speedbird620/Yet-another-simulator-chair/dxf/D1a.dxf

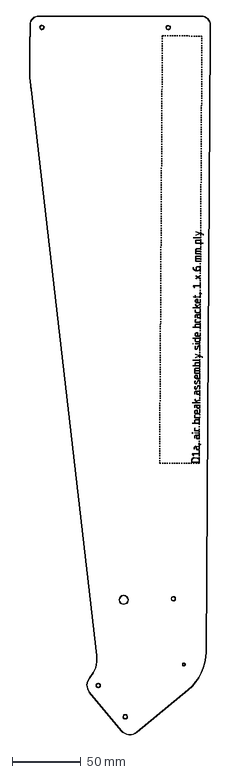
[picture p16: CAD file, 2024-12-31]
dxf/D1a.dxf
130.9 x 521.2 mm
