speedbird620/Yet-another-simulator-chair/stl/F12.stl

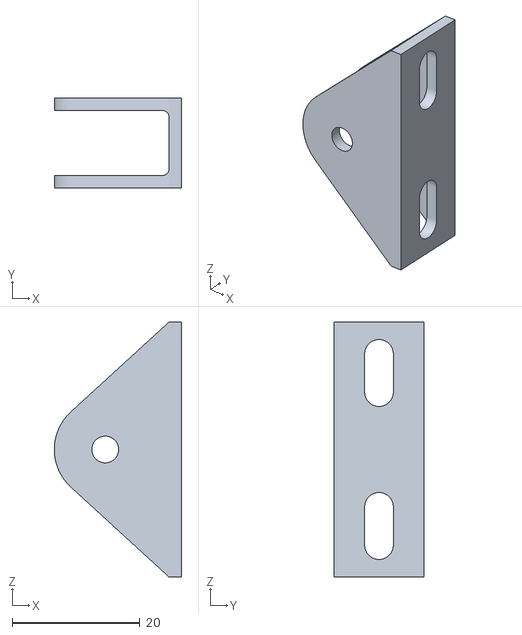
[picture p17: CAD file, 2025-11-08]
stl/F12.stl
20.0 x 14.2 x 40.0
