speedbird620/Yet-another-simulator-chair/dxf/A5.dxf

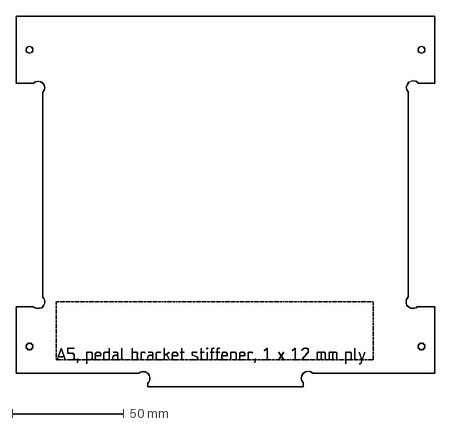
[picture p18: CAD file, 2024-12-29]
dxf/A5.dxf
187.7 x 166.0 mm
