speedbird620/Yet-another-simulator-chair/stl/F3.stl

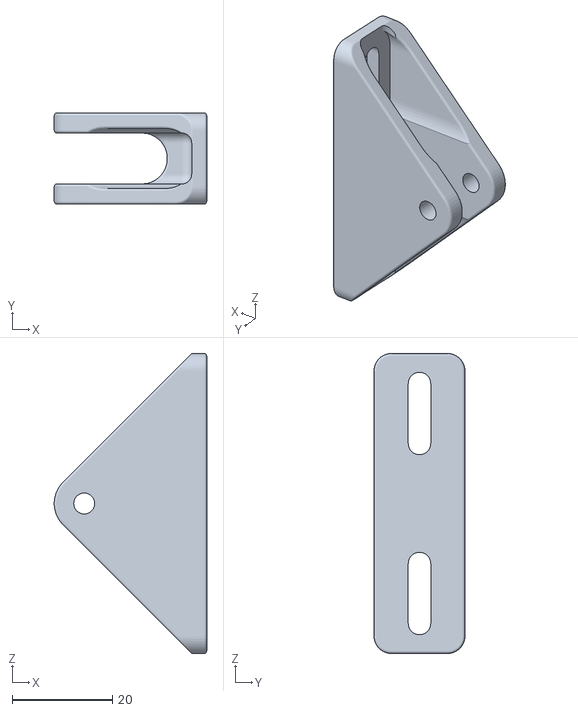
[picture p19: CAD file, 2025-11-08]
stl/F3.stl
30.5 x 18.2 x 60.0
