speedbird620/Yet-another-simulator-chair/dxf/B10.dxf

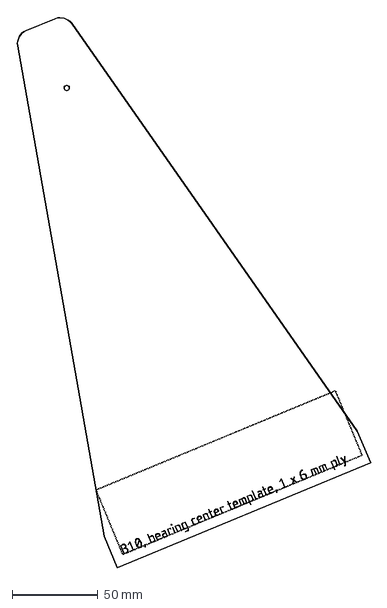
[picture p20: CAD file, 2024-12-22]
dxf/B10.dxf
206.6 x 321.9 mm
