speedbird620/Yet-another-simulator-chair/stl/H1.stl

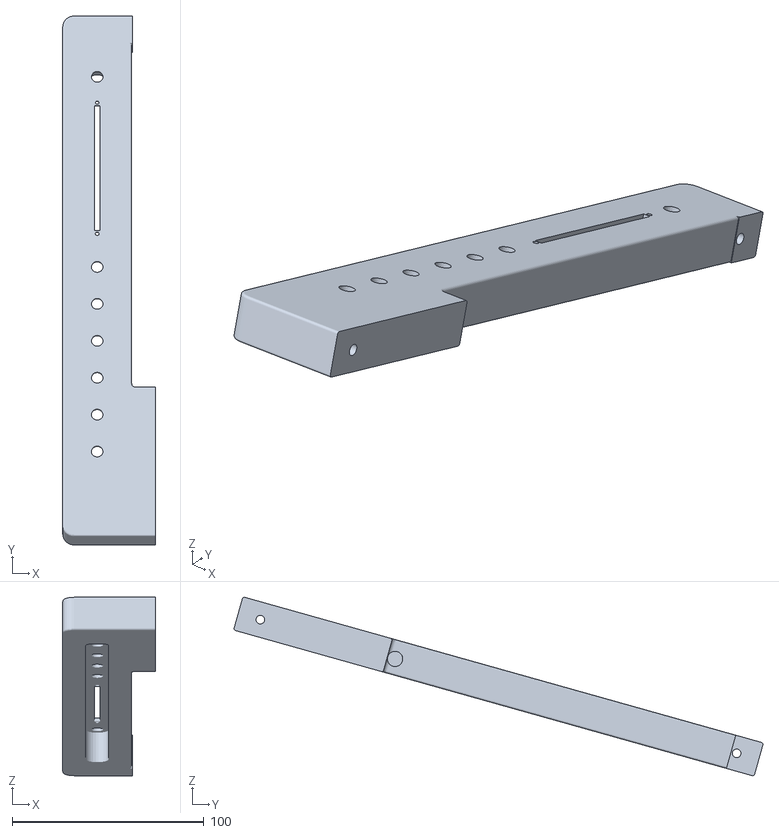
[picture p21: CAD file, 2025-10-26]
stl/H1.stl
48.3 x 275.9 x 93.1
