speedbird620/Yet-another-simulator-chair/dxf/C2.dxf

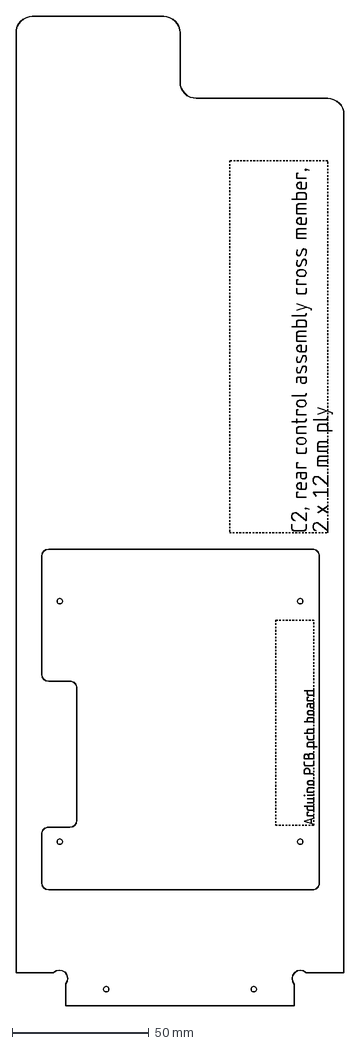
[picture p22: CAD file, 2024-12-13]
dxf/C2.dxf
120.0 x 362.0 mm
