speedbird620/Yet-another-simulator-chair/stl/H5.stl

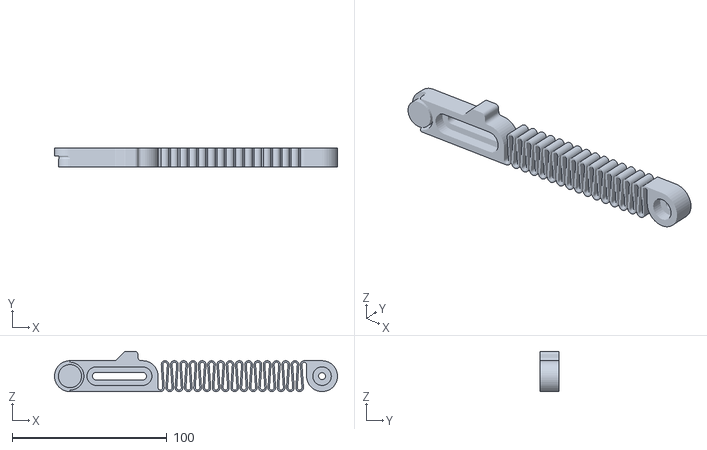
[picture p23: CAD file, 2024-12-18]
stl/H5.stl
183.0 x 12.0 x 26.0
