speedbird620/Yet-another-simulator-chair/dxf/B3.dxf

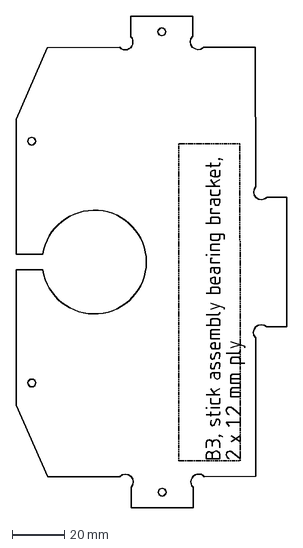
[picture p24: CAD file, 2024-12-13]
dxf/B3.dxf
104.1 x 188.9 mm
