speedbird620/Yet-another-simulator-chair/stl/H7.stl

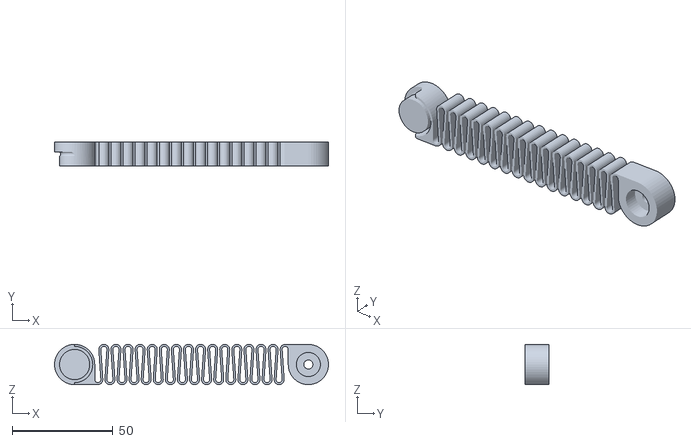
[picture p25: CAD file, 2024-12-18]
stl/H7.stl
136.0 x 12.0 x 20.0
