speedbird620/Yet-another-simulator-chair/dxf/A2.dxf

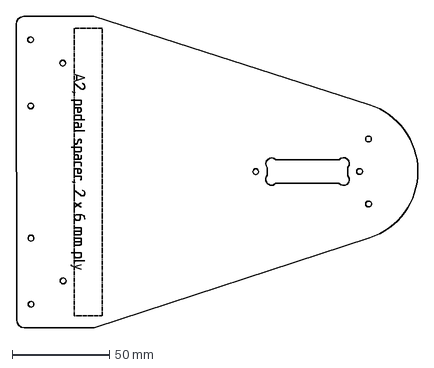
[picture p26: CAD file, 2024-12-13]
dxf/A2.dxf
206.7 x 160.1 mm
