speedbird620/Yet-another-simulator-chair/stl/F8.stl

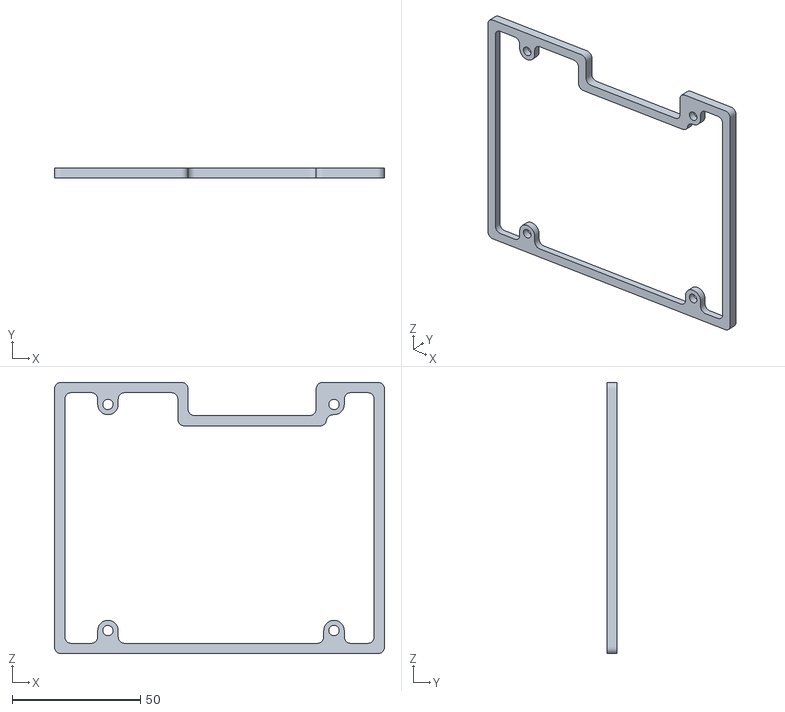
[picture p27: CAD file, 2024-12-17]
stl/F8.stl
128.5 x 4.00 x 105.6
