speedbird620/Yet-another-simulator-chair/dxf/B1.dxf

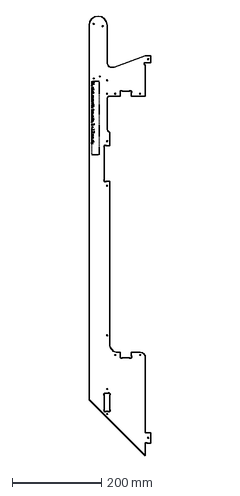
[picture p28: CAD file, 2024-12-13]
dxf/B1.dxf
138.0 x 985.4 mm
