speedbird620/Yet-another-simulator-chair/stl/H4.stl

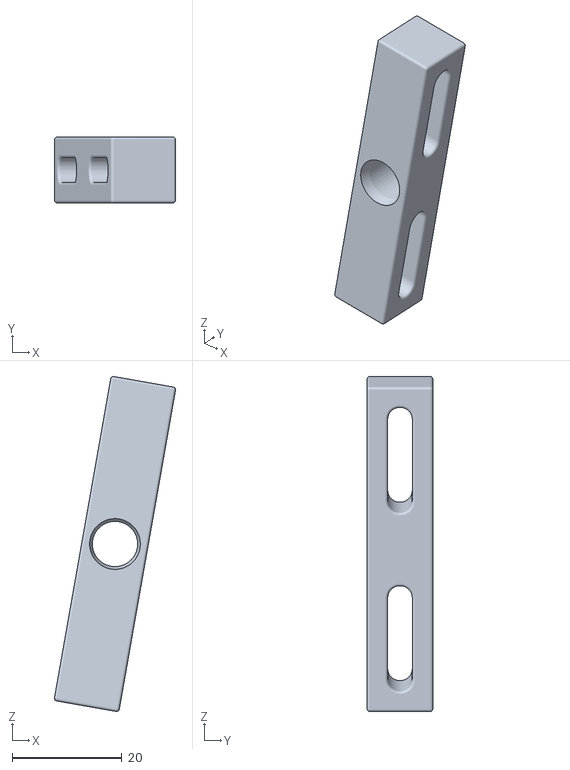
[picture p29: CAD file, 2024-12-15]
stl/H4.stl
22.1 x 12.0 x 61.0
