speedbird620/Yet-another-simulator-chair/dxf/A4.dxf

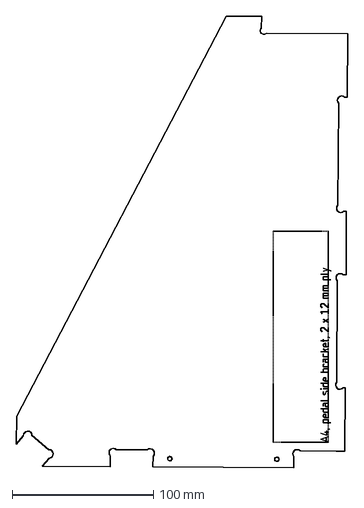
[picture p30: CAD file, 2024-12-13]
dxf/A4.dxf
234.7 x 320.0 mm
