speedbird620/Yet-another-simulator-chair/stl/H3.stl

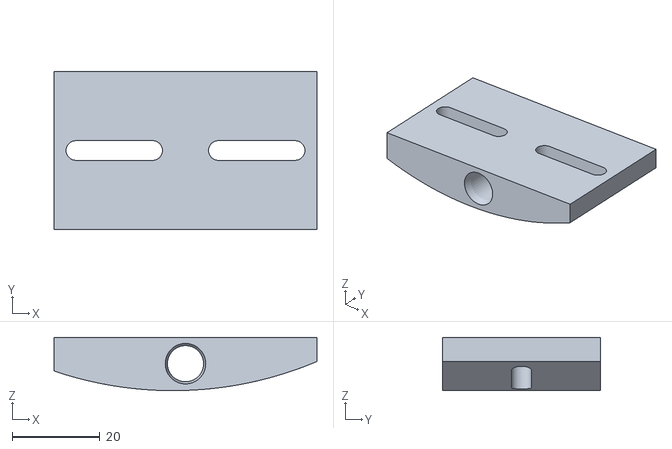
[picture p31: CAD file, 2024-12-15]
stl/H3.stl
60.0 x 36.0 x 12.1
