speedbird620/Yet-another-simulator-chair/dxf/B7.dxf

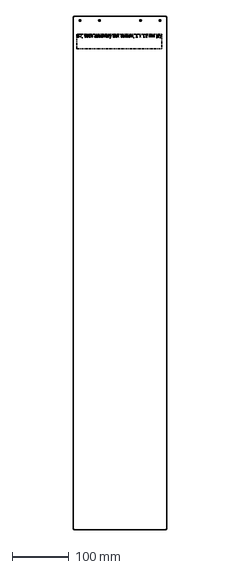
[picture p32: CAD file, 2024-12-13]
dxf/B7.dxf
165.0 x 906.5 mm
