speedbird620/Yet-another-simulator-chair/stl/G1.stl

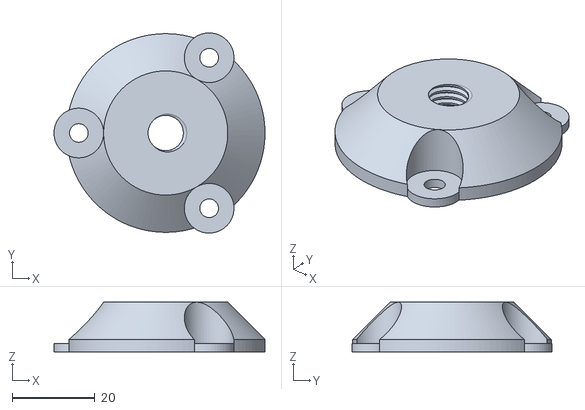
[picture p33: CAD file, 2024-12-07]
stl/G1.stl
51.0 x 48.4 x 12.0
