speedbird620/Yet-another-simulator-chair/dxf/C3.dxf

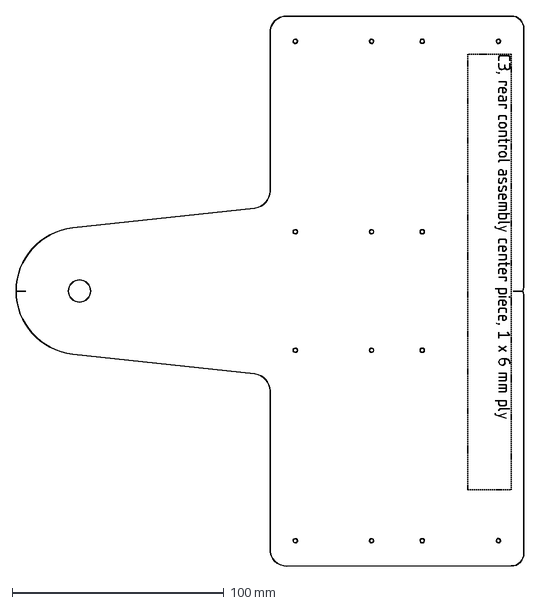
[picture p34: CAD file, 2024-12-13]
dxf/C3.dxf
240.0 x 260.0 mm
