speedbird620/Yet-another-simulator-chair/stl/F5.stl

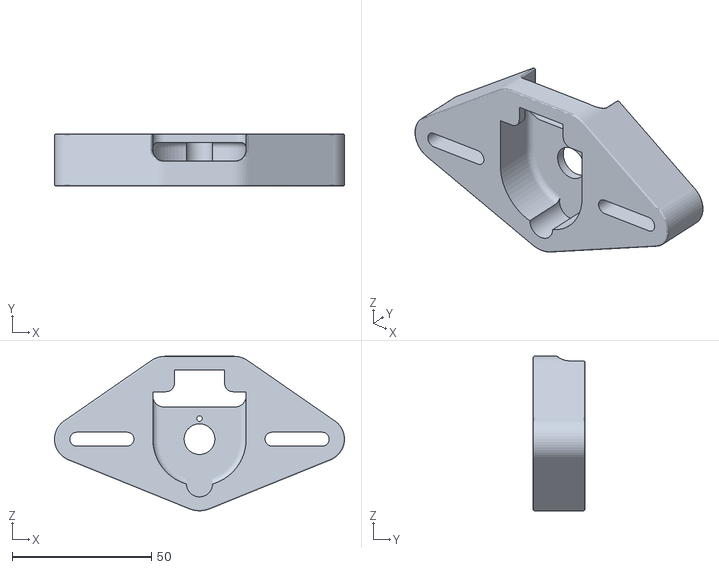
[picture p35: CAD file, 2024-12-04]
stl/F5.stl
104.0 x 18.6 x 55.4
