speedbird620/Yet-another-simulator-chair/dxf/E9.dxf

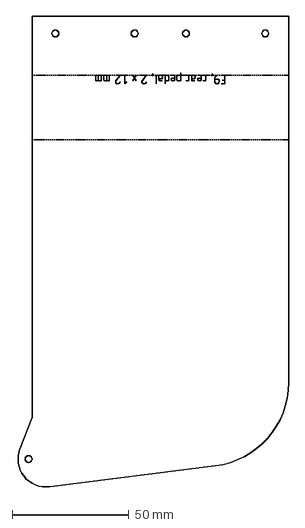
[picture p36: CAD file, 2024-12-13]
dxf/E9.dxf
116.7 x 202.4 mm
