speedbird620/Yet-another-simulator-chair/stl/G3.stl

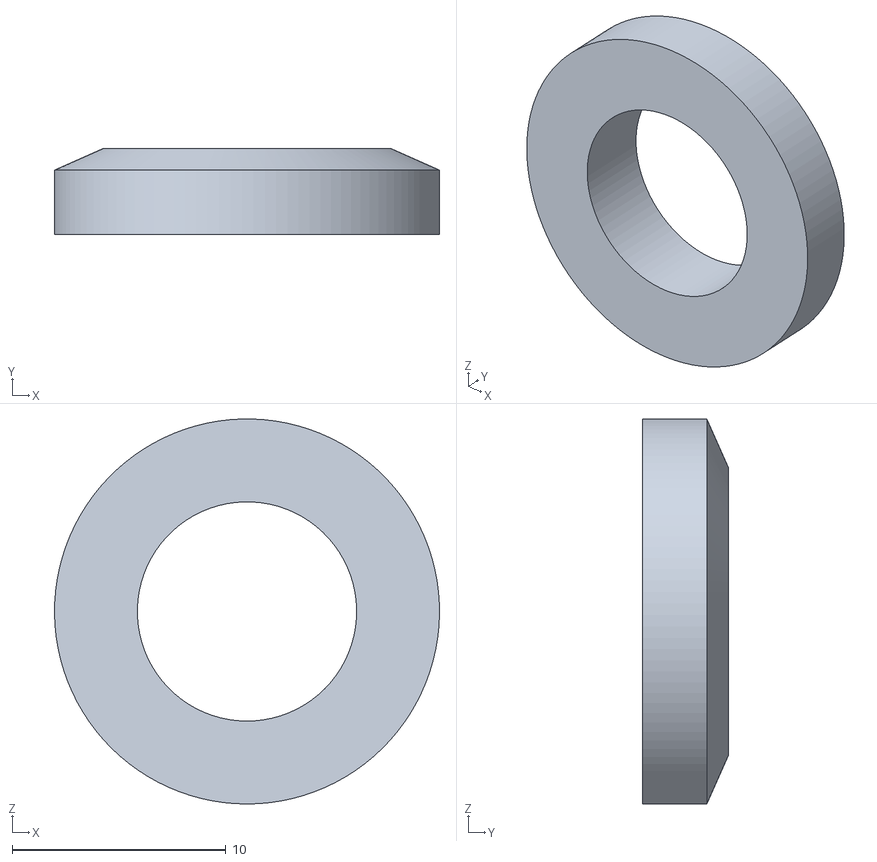
[picture p37: CAD file, 2024-12-03]
stl/G3.stl
18.0 x 4.00 x 18.0
