speedbird620/Yet-another-simulator-chair/dxf/B5.dxf

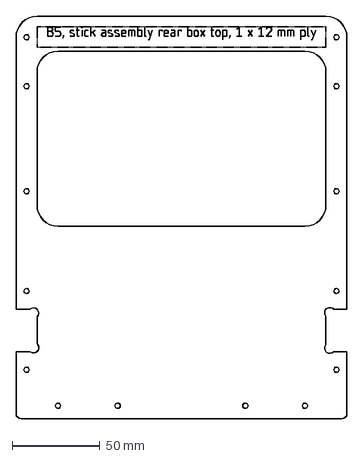
[picture p38: CAD file, 2024-12-13]
dxf/B5.dxf
189.0 x 230.0 mm
