speedbird620/Yet-another-simulator-chair/stl/G2.stl

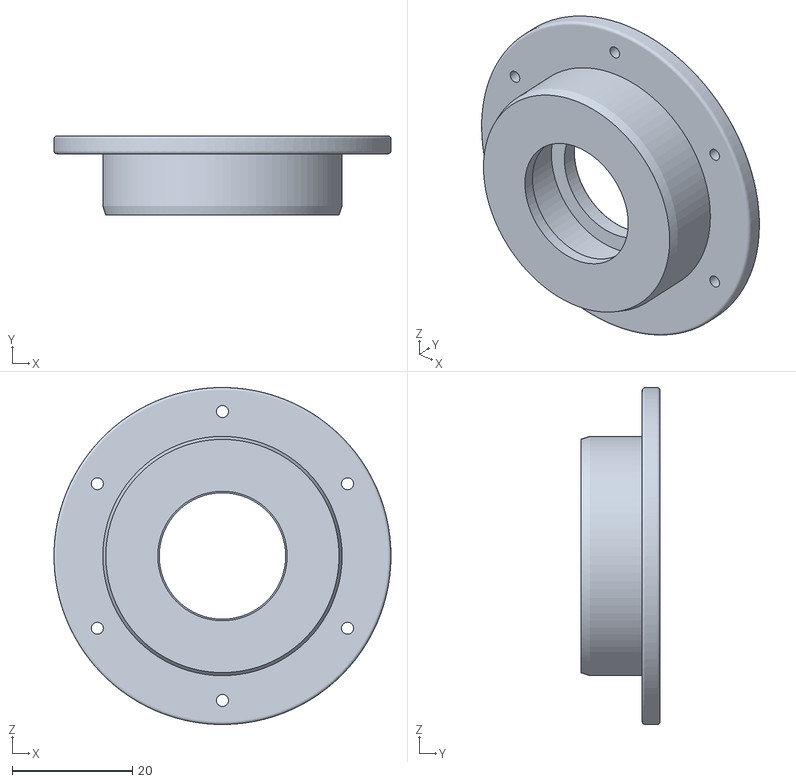
[picture p39: CAD file, 2024-12-03]
stl/G2.stl
56.0 x 13.2 x 56.0
