speedbird620/Yet-another-simulator-chair/dxf/E1.dxf

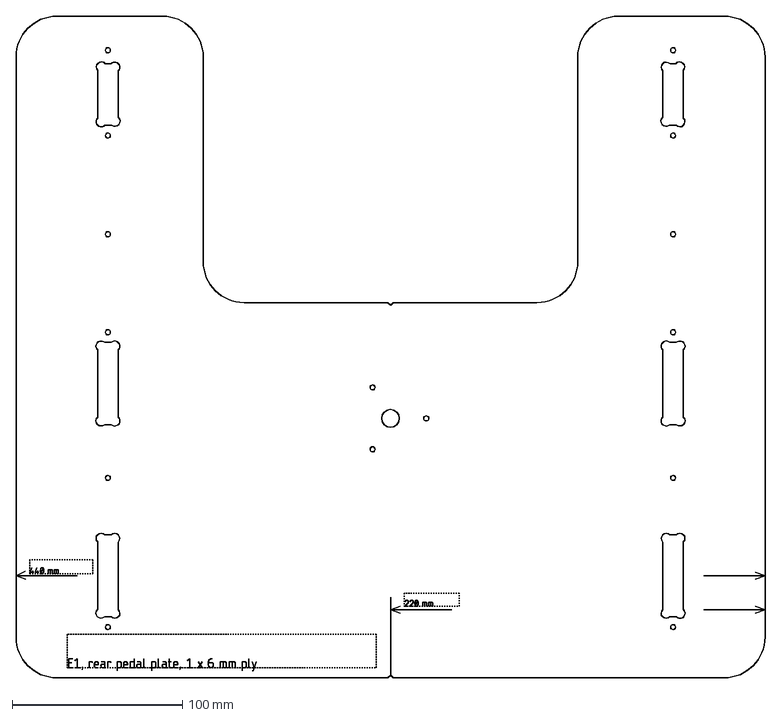
[picture p40: CAD file, 2024-12-13]
dxf/E1.dxf
440.0 x 388.7 mm
