speedbird620/Yet-another-simulator-chair/stl/F4.stl

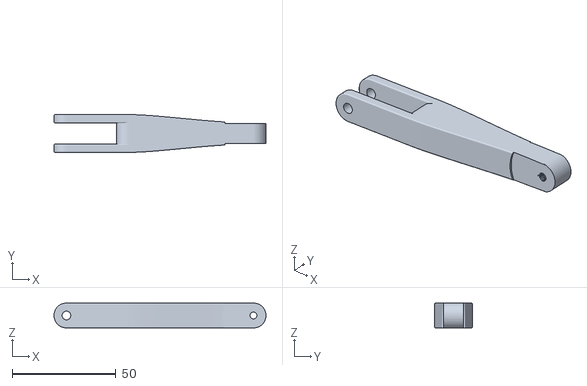
[picture p41: CAD file, 2024-12-03]
stl/F4.stl
102.0 x 18.2 x 12.0
