speedbird620/Yet-another-simulator-chair/dxf/E7.dxf

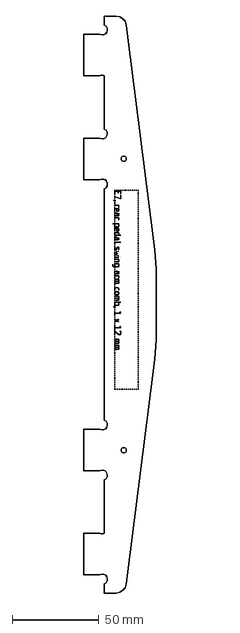
[picture p42: CAD file, 2024-12-13]
dxf/E7.dxf
42.0 x 333.1 mm
