speedbird620/Yet-another-simulator-chair/stl/F2.stl

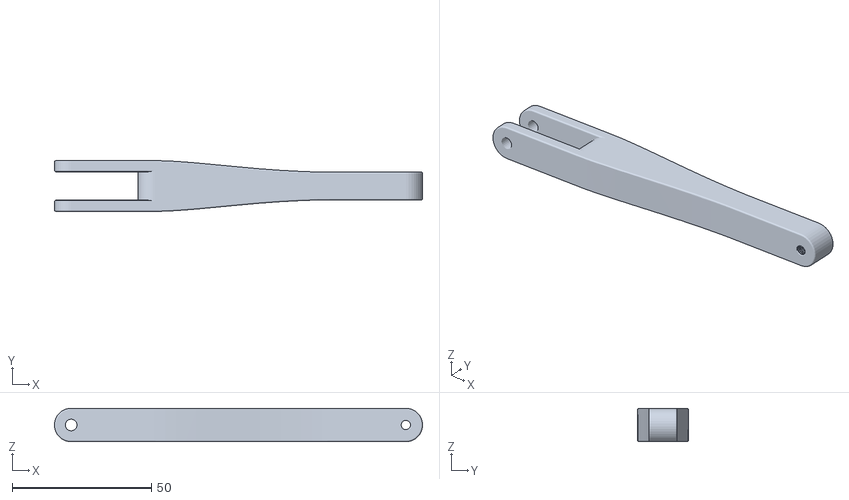
[picture p43: CAD file, 2024-08-14]
stl/F2.stl
132.0 x 18.2 x 12.0
