speedbird620/Yet-another-simulator-chair/dxf/E6.dxf

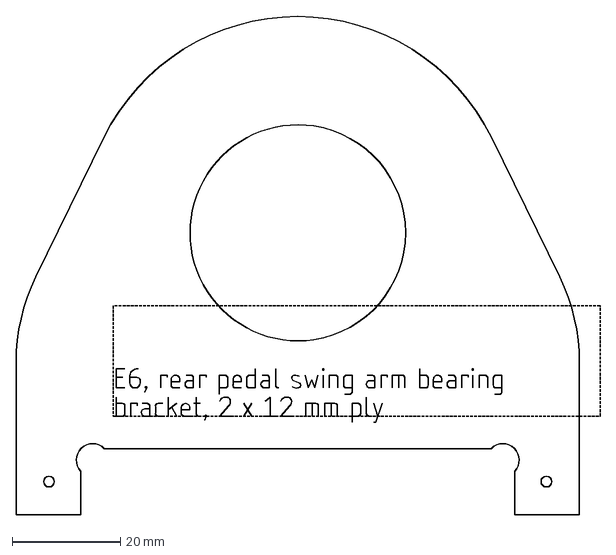
[picture p44: CAD file, 2024-12-13]
dxf/E6.dxf
108.0 x 92.1 mm
