speedbird620/Yet-another-simulator-chair/dxf/A6.dxf

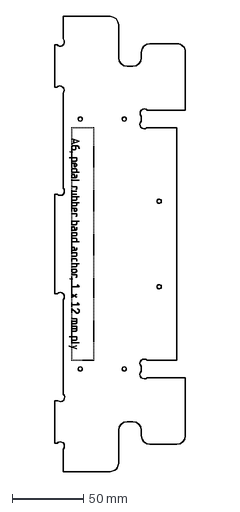
[picture p45: CAD file, 2024-12-13]
dxf/A6.dxf
92.0 x 320.0 mm
