speedbird620/Yet-another-simulator-chair/dxf/A8.dxf

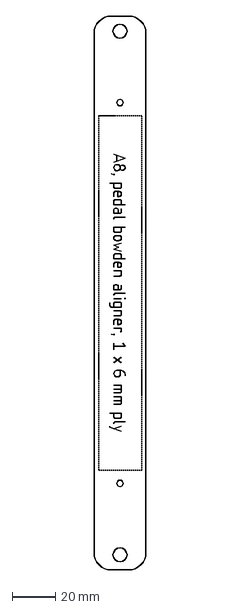
[picture p46: CAD file, 2024-12-13]
dxf/A8.dxf
24.0 x 255.7 mm
