speedbird620/Yet-another-simulator-chair/dxf/D5.dxf

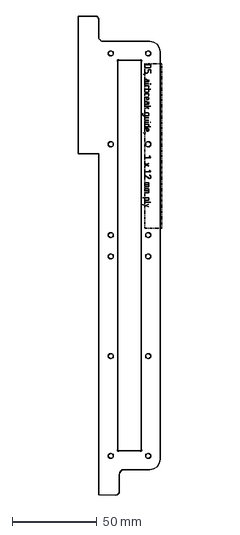
[picture p47: CAD file, 2024-12-13]
dxf/D5.dxf
49.2 x 282.0 mm
