speedbird620/Yet-another-simulator-chair/dxf/A7.dxf

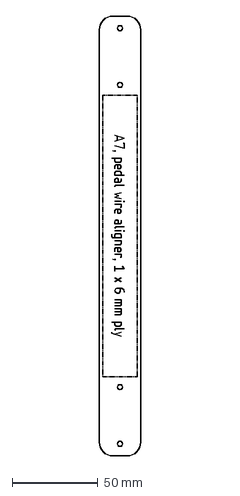
[picture p48: CAD file, 2024-12-13]
dxf/A7.dxf
24.0 x 255.7 mm
