speedbird620/Yet-another-simulator-chair/dxf/A1.dxf

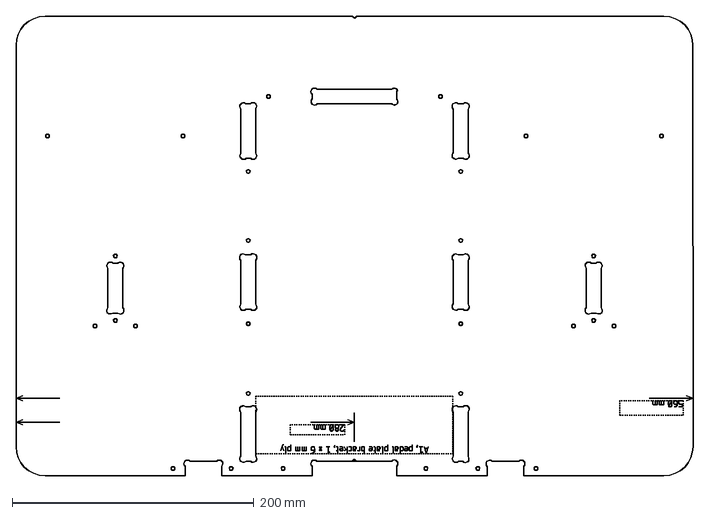
[picture p49: CAD file, 2024-12-13]
dxf/A1.dxf
560.0 x 380.0 mm
