speedbird620/Yet-another-simulator-chair/dxf/C1.dxf

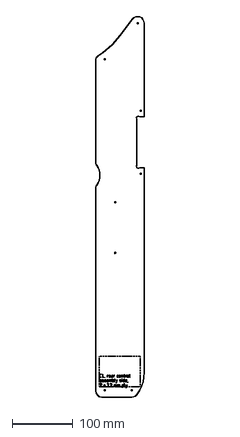
[picture p50: CAD file, 2024-12-13]
dxf/C1.dxf
80.0 x 628.1 mm
