speedbird620/Yet-another-simulator-chair/dxf/D1.dxf

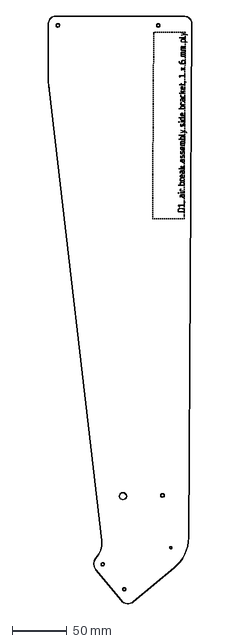
[picture p51: CAD file, 2024-12-13]
dxf/D1.dxf
130.9 x 535.2 mm
