speedbird620/Yet-another-simulator-chair/dxf/D6.dxf

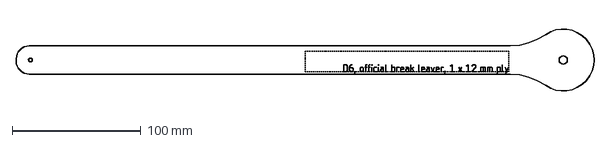
[picture p52: CAD file, 2024-12-13]
dxf/D6.dxf
451.0 x 53.3 mm
