speedbird620/Yet-another-simulator-chair/dxf/E3.dxf

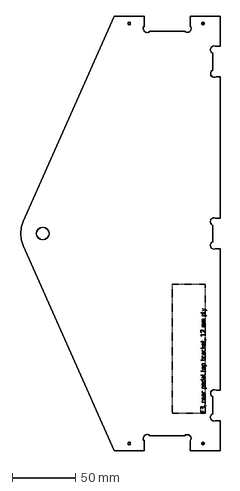
[picture p53: CAD file, 2024-12-13]
dxf/E3.dxf
158.5 x 344.0 mm
