speedbird620/Yet-another-simulator-chair/dxf/D4.dxf

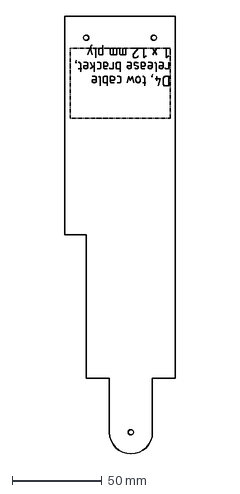
[picture p54: CAD file, 2024-12-13]
dxf/D4.dxf
61.8 x 243.8 mm
