speedbird620/Yet-another-simulator-chair/dxf/E5.dxf

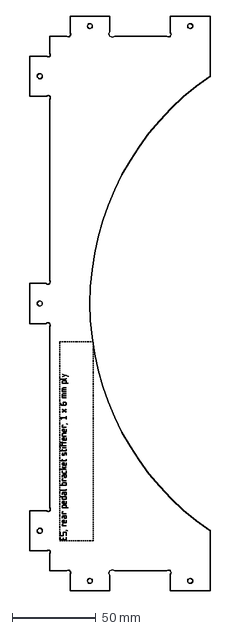
[picture p55: CAD file, 2024-12-13]
dxf/E5.dxf
108.0 x 344.0 mm
