speedbird620/Yet-another-simulator-chair/dxf/E8.dxf

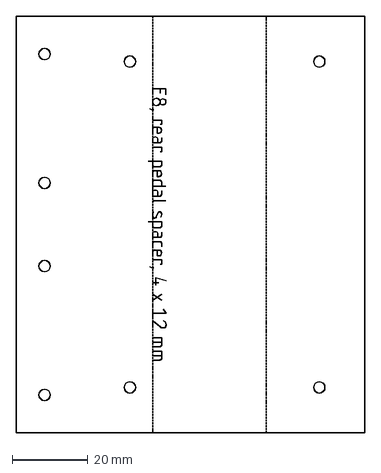
[picture p56: CAD file, 2024-12-13]
dxf/E8.dxf
92.0 x 110.0 mm
