speedbird620/Yet-another-simulator-chair/dxf/B4.dxf

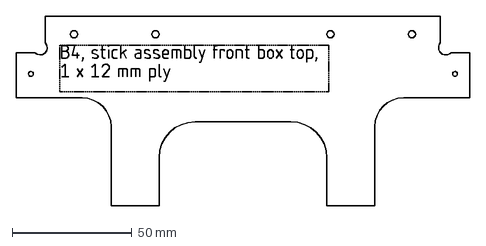
[picture p57: CAD file, 2024-12-13]
dxf/B4.dxf
189.1 x 79.0 mm
