speedbird620/Yet-another-simulator-chair/dxf/B8.dxf

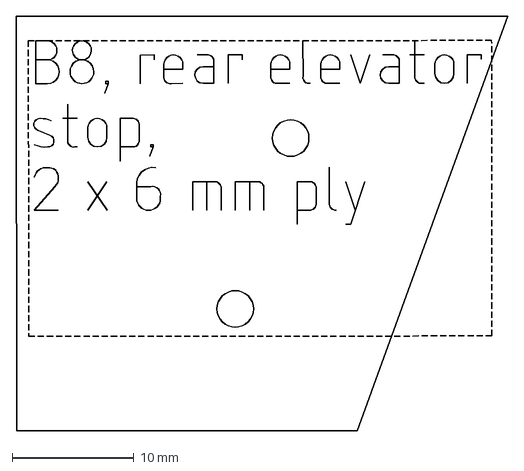
[picture p58: CAD file, 2024-12-13]
dxf/B8.dxf
40.3 x 34.0 mm
