speedbird620/Yet-another-simulator-chair/dxf/B2.dxf

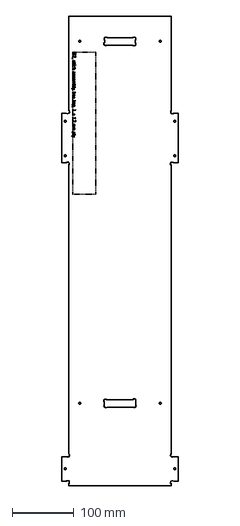
[picture p59: CAD file, 2024-12-13]
dxf/B2.dxf
189.0 x 760.0 mm
