speedbird620/Yet-another-simulator-chair/dxf/E4.dxf

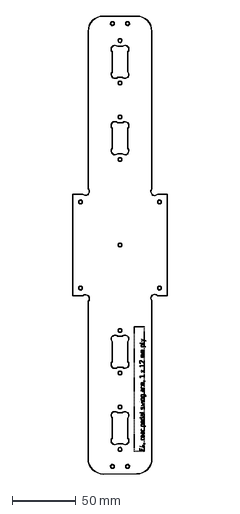
[picture p60: CAD file, 2024-12-13]
dxf/E4.dxf
74.0 x 360.0 mm
