speedbird620/Yet-another-simulator-chair/dxf/D3.dxf

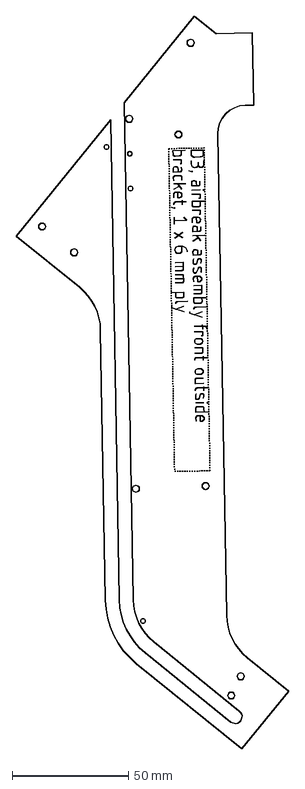
[picture p61: CAD file, 2024-12-13]
dxf/D3.dxf
117.1 x 315.1 mm
