speedbird620/Yet-another-simulator-chair/dxf/E2.dxf

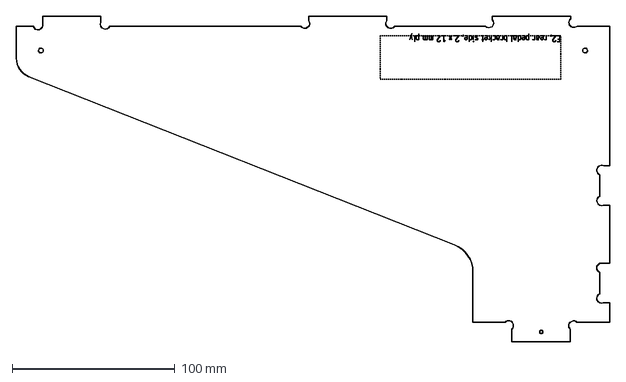
[picture p62: CAD file, 2024-12-13]
dxf/E2.dxf
364.7 x 200.0 mm
