speedbird620/Yet-another-simulator-chair/dxf/B9.dxf

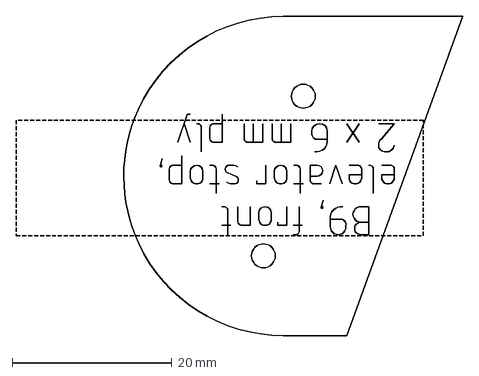
[picture p63: CAD file, 2024-12-13]
dxf/B9.dxf
56.0 x 40.0 mm
