speedbird620/Yet-another-simulator-chair/dxf/D2.dxf

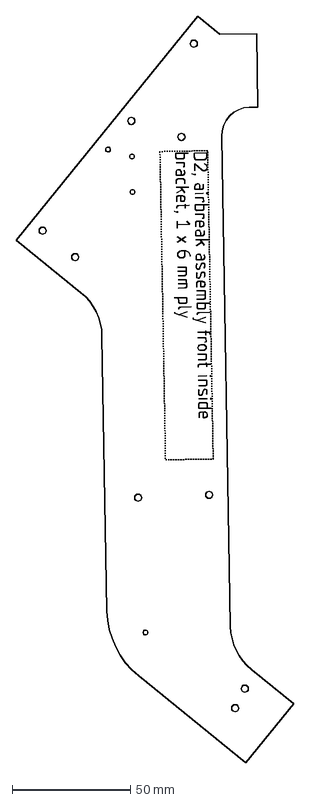
[picture p64: CAD file, 2024-12-13]
dxf/D2.dxf
117.1 x 315.1 mm
