speedbird620/Yet-another-simulator-chair/dxf/A9.dxf

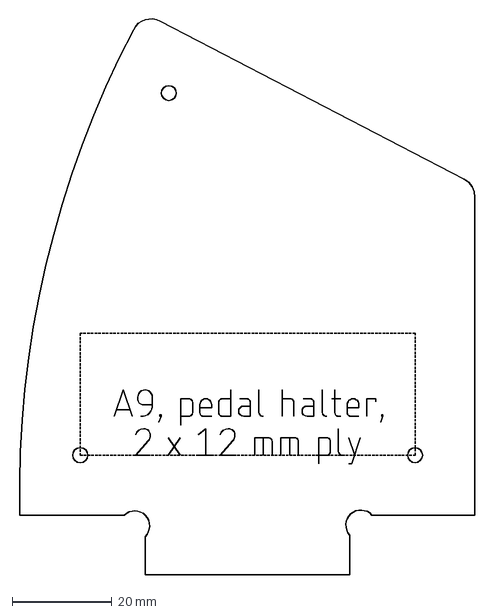
[picture p65: CAD file, 2024-12-13]
dxf/A9.dxf
92.0 x 112.0 mm
