speedbird620/Yet-another-simulator-chair/dxf/B6.dxf

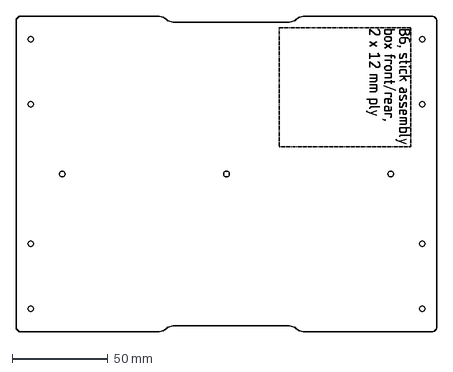
[picture p66: CAD file, 2024-12-13]
dxf/B6.dxf
220.0 x 165.0 mm
