speedbird620/Yet-another-simulator-chair/dxf/A3.dxf

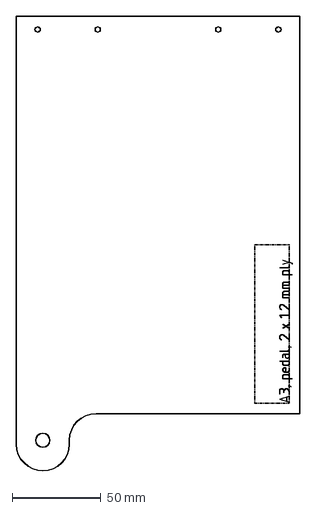
[picture p67: CAD file, 2024-12-13]
dxf/A3.dxf
160.0 x 256.7 mm
